IyanekiB/ECE1895-Bop-It/Components/OLED/OLED_counter_replay/OLED_counter_replay.ino

#include <Wire.h>
#include <Adafruit_GFX.h>
#include <Adafruit_SSD1306.h>

#define OLED_WIDTH       128
#define OLED_HEIGHT       64
#define OLED_RESET        -1    // not used

#define SWITCH_PIN        2     // START / Power toggle
#define MODE_BTN_PIN      3     // Mode select
#define OLED_POWER_PIN    4
#define BUZZER_PIN        5

#define SWING_PIN         A1    // Accelerometer (analog)
#define SHEATH_PIN        6    // Sheath switch (digital)
#define BOOST_PIN         7    // Boost button (digital)
#define SWING_THRESHOLD   600

Adafruit_SSD1306 display(OLED_WIDTH, OLED_HEIGHT, &Wire, OLED_RESET);

int  lastModeState  = HIGH;
bool oledOn         = false;
uint8_t modeCount   = 1;       // 1=Easy,2=Medium,3=Hard

//------------------------------------------------------------------------------
// Detect a single falling edge on SWITCH_PIN (with debounce). Returns true only
// once per physical press, not while held.
//
bool checkPowerToggle() {
  static int last = HIGH;
  int cur = digitalRead(SWITCH_PIN);
  if (cur != last) {
    delay(50);
    cur = digitalRead(SWITCH_PIN);
    if (cur != last && cur == LOW) {
      last = cur;
      return true;
    }
  }
  last = cur;
  return false;
}

void setup() {
  Serial.begin(9600);

  pinMode(SWITCH_PIN,     INPUT_PULLUP);
  pinMode(MODE_BTN_PIN,   INPUT_PULLUP);
  pinMode(OLED_POWER_PIN, OUTPUT);
  pinMode(BUZZER_PIN,     OUTPUT);
  pinMode(SHEATH_PIN,     INPUT_PULLUP);
  pinMode(BOOST_PIN,      INPUT_PULLUP);
  digitalWrite(OLED_POWER_PIN, LOW);
  digitalWrite(BUZZER_PIN,   LOW);

  if (!display.begin(SSD1306_SWITCHCAPVCC, 0x3C)) {
    Serial.println(F("OLED init failed"));
    while (1);
  }
  display.clearDisplay();
  display.display();
  randomSeed(analogRead(A5));
}

void loop() {
  if (checkPowerToggle()) {
    oledOn = !oledOn;
    Serial.println(oledOn ? "OLED ON" : "OLED OFF");
    if (oledOn)      powerUpAndSelectMode();
    else             powerDownOLED();
  }
}

void powerUpAndSelectMode() {
  digitalWrite(OLED_POWER_PIN, HIGH);
  delay(10);

  // Title screen (interruptible)
  display.clearDisplay();
  display.setTextSize(2);
  display.setTextColor(WHITE);
  display.setCursor(0,0);
  display.println("Bop-It!");
  display.display();
  {
    unsigned long t0 = millis();
    while (millis() - t0 < 2000) {
      if (checkPowerToggle()) {
        oledOn = false;
        powerDownOLED();
        return;
      }
    }
  }

  // Mode menu
  modeCount = 1;
  showMenu();
  unsigned long lastPress = millis();
  lastModeState = digitalRead(MODE_BTN_PIN);
  while (millis() - lastPress < 5000) {
    if (checkPowerToggle()) {
      oledOn = false;
      powerDownOLED();
      return;
    }
    int m = digitalRead(MODE_BTN_PIN);
    if (m != lastModeState) {
      delay(50);
      m = digitalRead(MODE_BTN_PIN);
      if (m == LOW) {
        modeCount = modeCount % 3 + 1;
        Serial.print("Mode = "); Serial.println(modeCount);
        showMenu();
        lastPress = millis();
      }
    }
    lastModeState = m;
  }

  // Confirm screen (interruptible)
  display.clearDisplay();
  display.setTextSize(2);
  display.setCursor(0,16);
  if      (modeCount==1) display.println("Easy Mode");
  else if (modeCount==2) display.println("Medium Mode");
  else                   display.println("Hard Mode");
  display.display();
  {
    unsigned long t0 = millis();
    while (millis() - t0 < 2000) {
      if (checkPowerToggle()) {
        oledOn = false;
        powerDownOLED();
        return;
      }
    }
  }

  runGame();
}

void runGame() {
  unsigned long interval = (modeCount==1?5000: modeCount==2?4000:3000);
  unsigned long lastCueTime = millis();
  int score = 0;

  while (oledOn) {
    // 1) Falling‐edge check to power off
    if (checkPowerToggle()) {
      Serial.println("OLED OFF during game");
      break;
    }

    // 2) Cue
    if (millis() - lastCueTime >= interval) {
      lastCueTime = millis();
      uint8_t cmd = random(1,4);
      const char* txt = (cmd==1?"Swing It!": cmd==2?"Sheath It!": "Boost It!");
      Serial.print("Command: "); Serial.println(txt);

      // Show command
      display.clearDisplay();
      display.setTextSize(2);
      display.setCursor(0,16);
      display.println(txt);
      display.display();

      // Beeps (interruptible per tone & pause)
      for (uint8_t i=0; i<cmd; i++) {
        if (checkPowerToggle()) {
          noTone(BUZZER_PIN);
          oledOn = false;
          powerDownOLED();
          return;
        }
        tone(BUZZER_PIN, 2000, 200);
        unsigned long beepStart = millis();
        while (millis() - beepStart < 200) {
          if (checkPowerToggle()) {
            noTone(BUZZER_PIN);
            oledOn = false;
            powerDownOLED();
            return;
          }
        }
        unsigned long pauseStart = millis();
        while (millis() - pauseStart < 250) {
          if (checkPowerToggle()) {
            noTone(BUZZER_PIN);
            oledOn = false;
            powerDownOLED();
            return;
          }
        }
      }
      noTone(BUZZER_PIN);

      // Wait for user response
      unsigned long start = millis();
      bool ok = false;
      while (millis() - start < interval) {
        if (checkPowerToggle()) {
          oledOn = false;
          powerDownOLED();
          return;
        }
        if (cmd==1 && analogRead(SWING_PIN) > SWING_THRESHOLD) { ok = true; break; }
        if (cmd==2 && digitalRead(SHEATH_PIN)==LOW)             { ok = true; break; }
        if (cmd==3 && digitalRead(BOOST_PIN)==LOW)              { ok = true; break; }
      }

      if (!ok) {
        showGameOver(score);
        return;
      }

      score++;
      Serial.print("Score: "); Serial.println(score);
    }
  }

  powerDownOLED();
}

void showMenu() {
  display.clearDisplay();
  display.setTextSize(1);
  display.setCursor(0,0);
  display.println("Select Mode:");
  for (uint8_t i=1; i<=3; i++) {
    display.setCursor(0, 16 + (i-1)*12);
    display.print(i==modeCount?"> ":"  ");
    display.print(i); display.print(") ");
    display.println(i==1?"Easy": i==2?"Medium":"Hard");
  }
  display.display();
}

void showGameOver(int finalScore) {
  // Display GAME OVER + score
  display.clearDisplay();
  display.setTextSize(2);
  display.setCursor(0,0);
  display.println("GAME OVER");
  display.setTextSize(1);
  display.setCursor(0,34);
  display.print("Score: ");
  display.println(finalScore);
  display.display();
  Serial.print("Final Score: "); Serial.println(finalScore);

  // 5s interruptible wait
  {
    unsigned long t0 = millis();
    while (millis() - t0 < 5000) {
      if (checkPowerToggle()) {
        oledOn = false;
        powerDownOLED();
        return;
      }
    }
  }

  // Two-option menu
  uint8_t option = 1;   // 1=Play Again, 2=Mode Select
  lastModeState = digitalRead(MODE_BTN_PIN);
  unsigned long lastPress = millis();
  showGameOverMenu(option);

  // 5s to toggle
  while (millis() - lastPress < 5000) {
    if (checkPowerToggle()) {
      oledOn = false;
      return;
    }
    int m = digitalRead(MODE_BTN_PIN);
    if (m != lastModeState) {
      delay(50);
      m = digitalRead(MODE_BTN_PIN);
      if (m == LOW) {
        option = (option % 2) + 1;
        showGameOverMenu(option);
        lastPress = millis();
      }
    }
    lastModeState = m;
  }

  // Act on choice
  if (option == 1)       runGame();
  else                   powerUpAndSelectMode();
}

void showGameOverMenu(uint8_t option) {
  display.clearDisplay();
  display.setTextSize(1);
  display.setCursor(0,0);
  display.println("Select Option:");
  display.setCursor(0,16);
  display.print(option==1?"> ":"  "); display.println("Play Again");
  display.setCursor(0,28);
  display.print(option==2?"> ":"  "); display.println("Mode Select");
  display.display();
}

void powerDownOLED() {
  display.clearDisplay();
  display.display();
  digitalWrite(OLED_POWER_PIN, LOW);
}
